RepRapLtd/Infinite-Z-Beam/Pix/20210806_100222.jpg

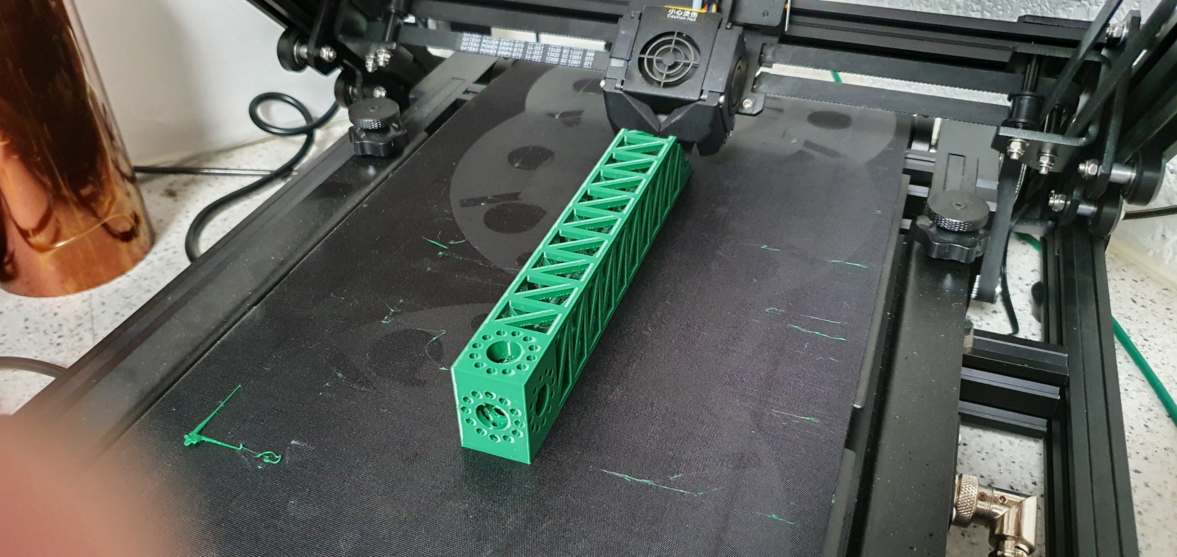
Pix/20210806_100222.jpg
