RepRapLtd/Infinite-Z-Beam/Pix/20210806_114202.jpg

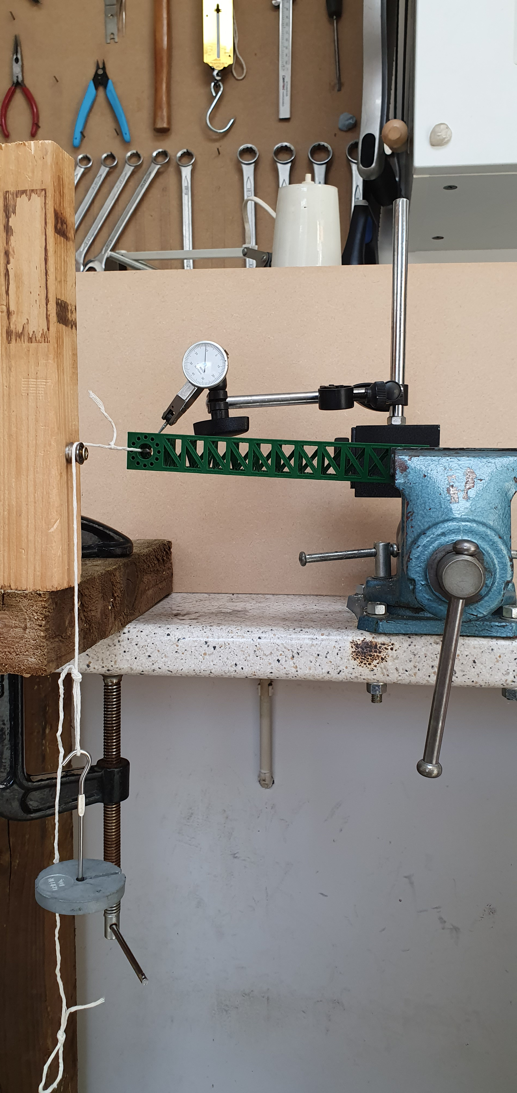
Pix/20210806_114202.jpg
