RepRapLtd/Infinite-Z-Beam/Pix/20210806_164224.jpg

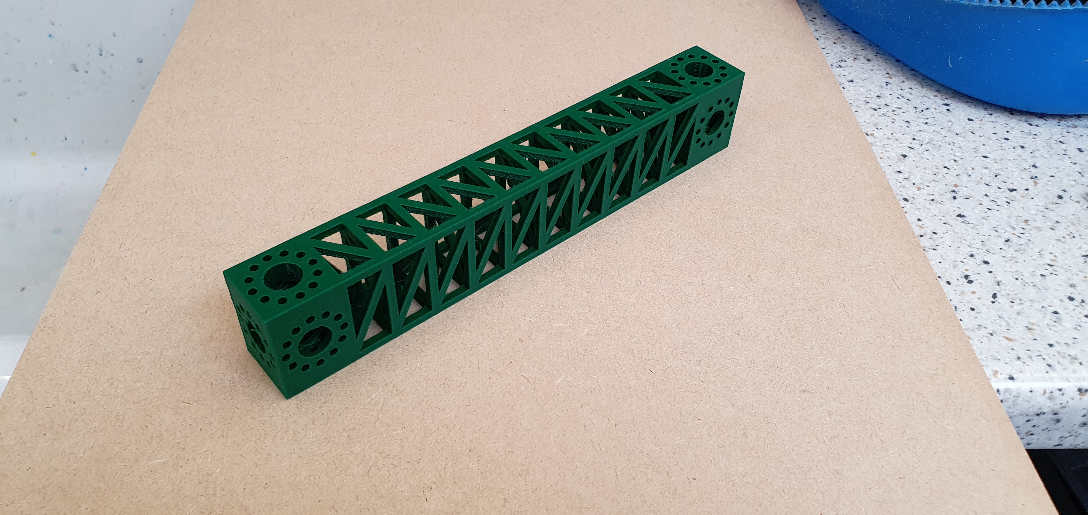
Pix/20210806_164224.jpg
