RepRapLtd/Infinite-Z-Beam/Pix/20210807_092451.jpg

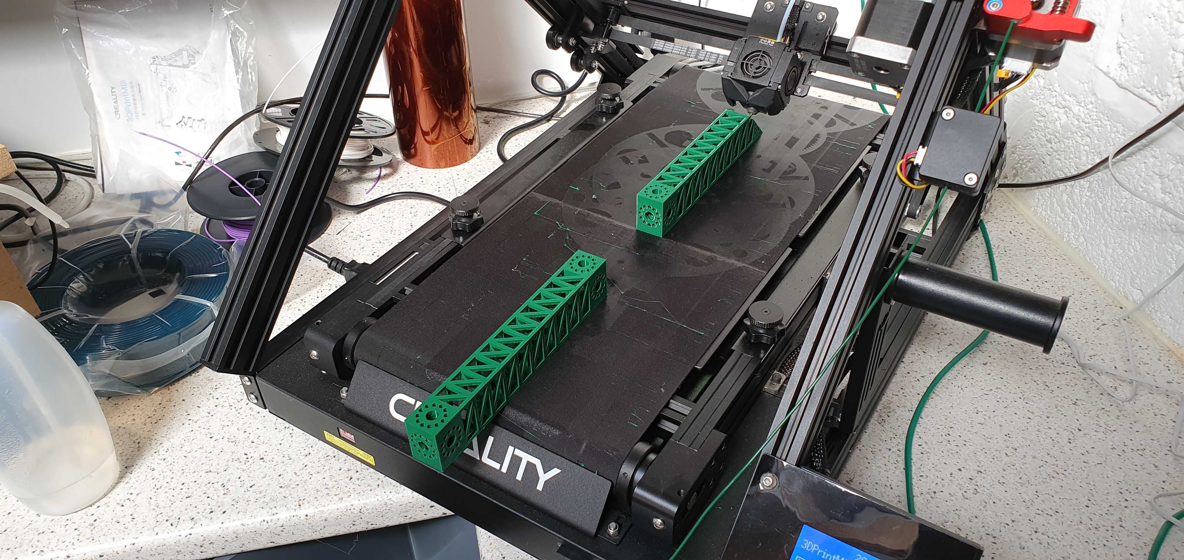
Pix/20210807_092451.jpg
