RepRapLtd/Infinite-Z-Beam/Pix/20210808_162842.jpg

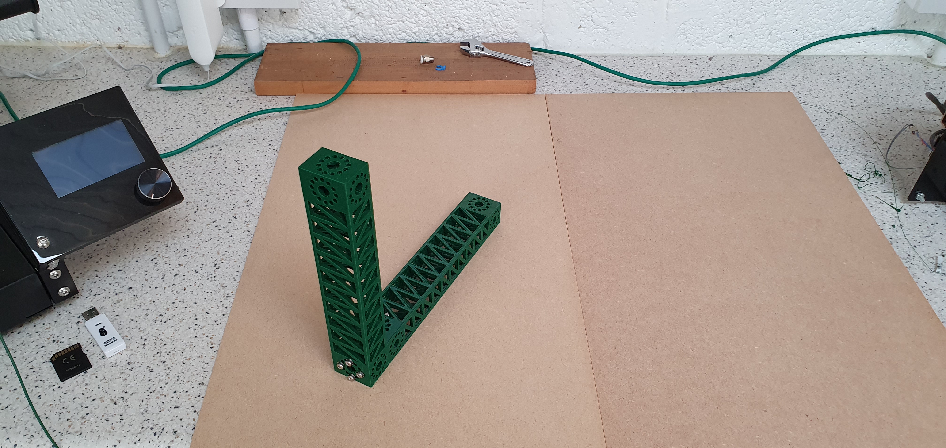
Pix/20210808_162842.jpg
